ChaeyongPark-KU/HaptiCraft/Hardware/Thermal Module/3_side-left.STL

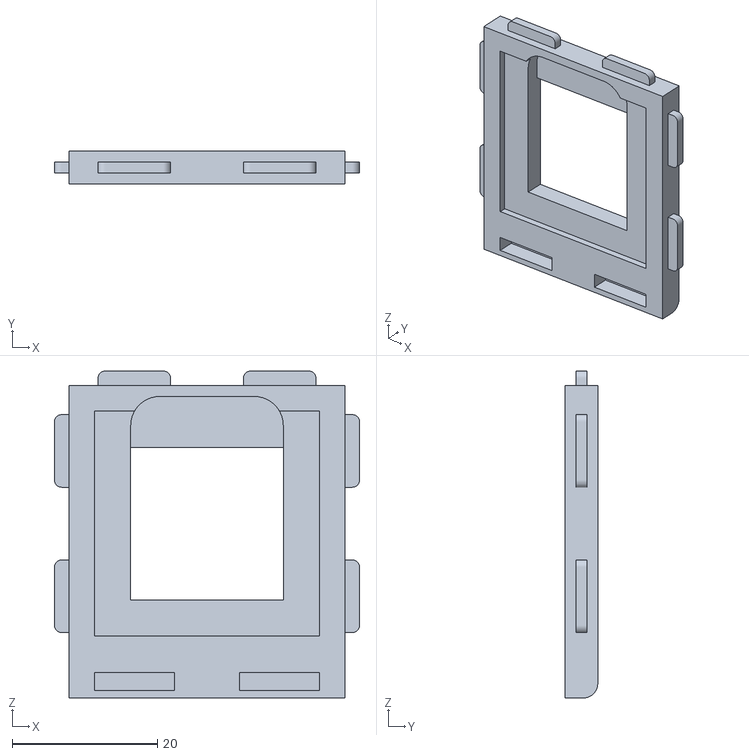
[picture p32: CAD file, 2026-03-29]
Hardware/Thermal Module/3_side-left.STL
42.0 x 4.50 x 45.0
