ChaeyongPark-KU/HaptiCraft/Hardware/Touch Module/3_touch pannel 1.STL

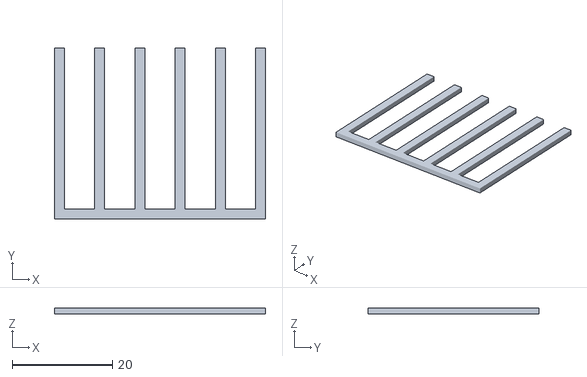
[picture p33: CAD file, 2026-03-29]
Hardware/Touch Module/3_touch pannel 1.STL
42.0 x 34.0 x 1.20
