ChaeyongPark-KU/HaptiCraft/Hardware/Tracking Module/3_rod 50mm.STL

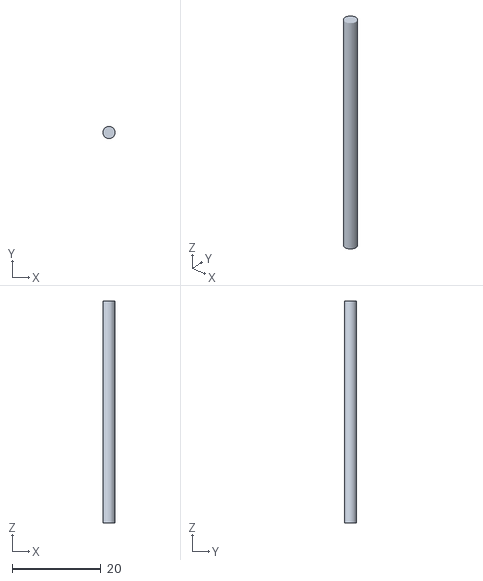
[picture p34: CAD file, 2026-03-29]
Hardware/Tracking Module/3_rod 50mm.STL
2.75 x 2.75 x 50.0
