ChaeyongPark-KU/HaptiCraft/Hardware/Variable Damping Actuator/5_plunger lower-part.STL

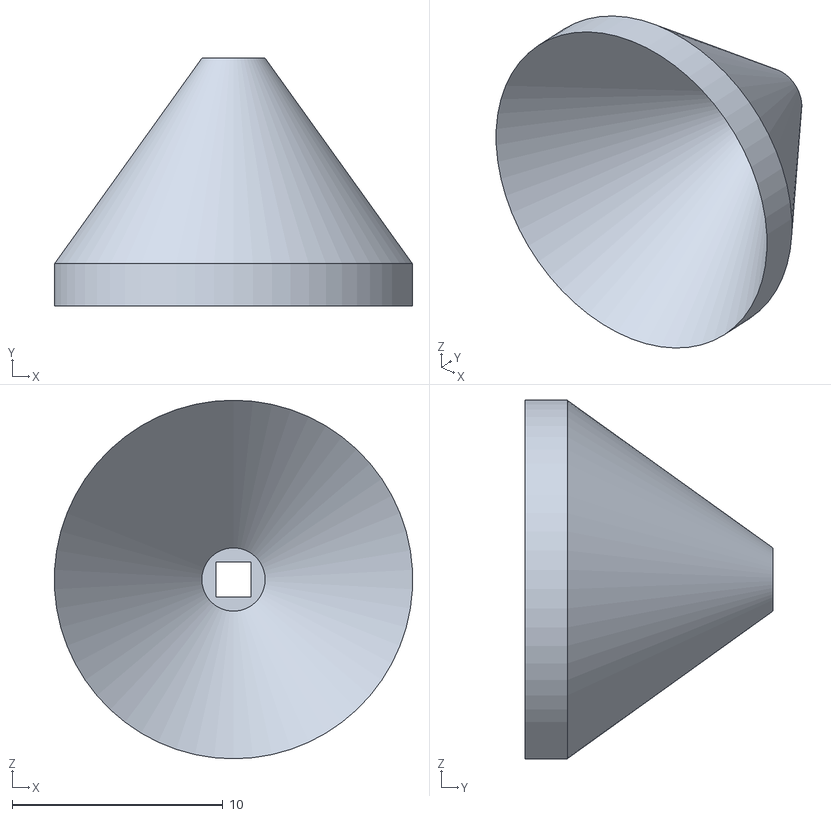
[picture p35: CAD file, 2026-03-31]
Hardware/Variable Damping Actuator/5_plunger lower-part.STL
17.0 x 11.8 x 17.0
