ChaeyongPark-KU/HaptiCraft/Hardware/Variable Inertia Module/8_internal circuit.STL

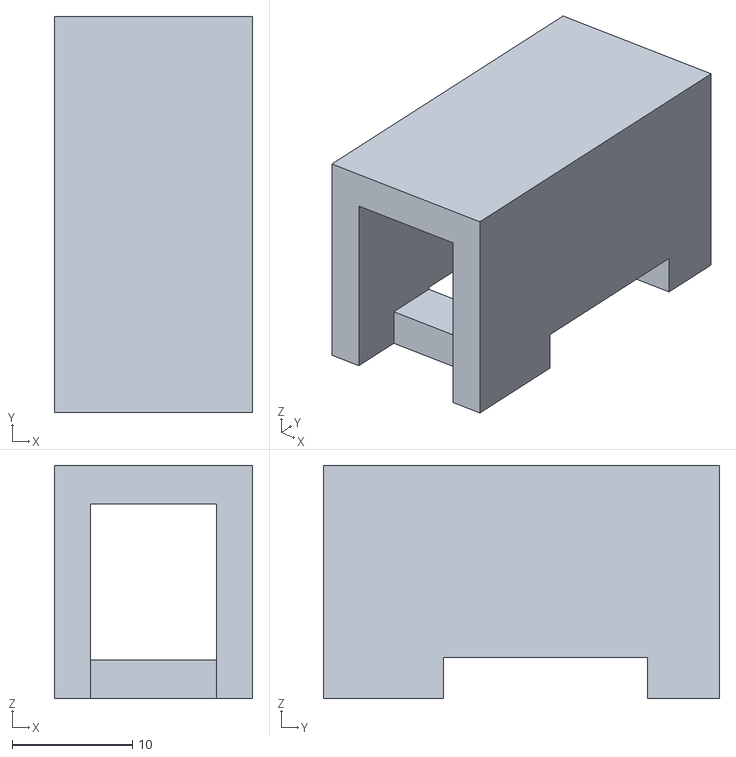
[picture p36: CAD file, 2026-03-29]
Hardware/Variable Inertia Module/8_internal circuit.STL
16.5 x 33.0 x 19.4
