ChaeyongPark-KU/HaptiCraft/Hardware/Vibration Module/2_side-front.STL

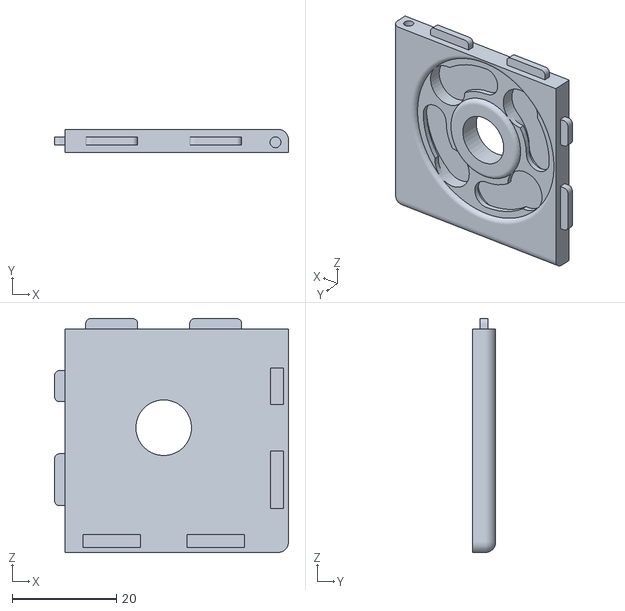
[picture p37: CAD file, 2026-03-29]
Hardware/Vibration Module/2_side-front.STL
45.0 x 4.50 x 45.0
