ChaeyongPark-KU/HaptiCraft/Hardware/Button Module/3_top.STL

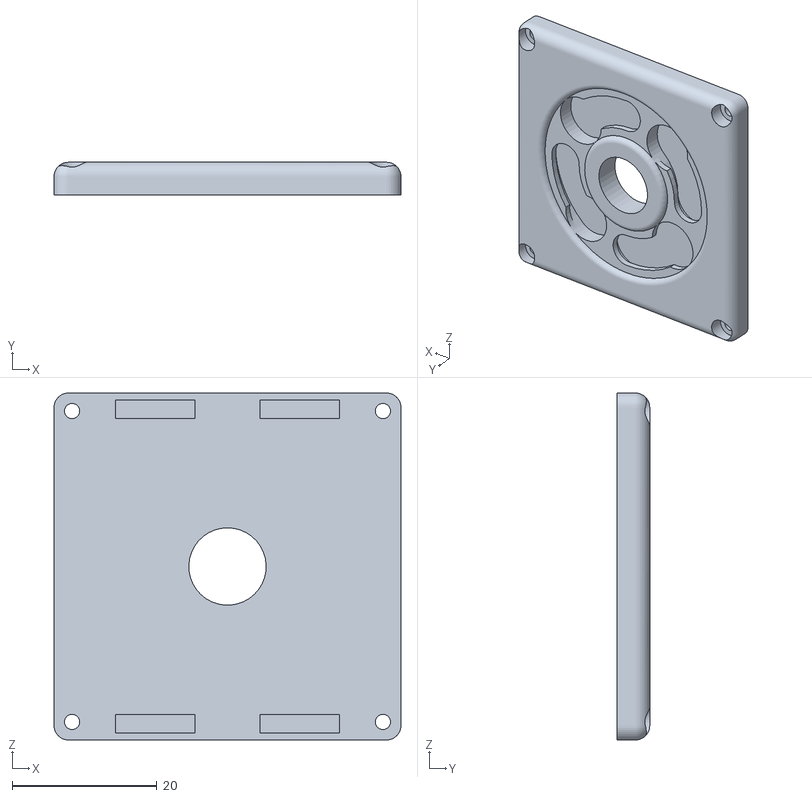
[picture p38: CAD file, 2026-03-29]
Hardware/Button Module/3_top.STL
48.0 x 4.50 x 48.0
