ChaeyongPark-KU/HaptiCraft/Hardware/Impact Module/6_top.STL

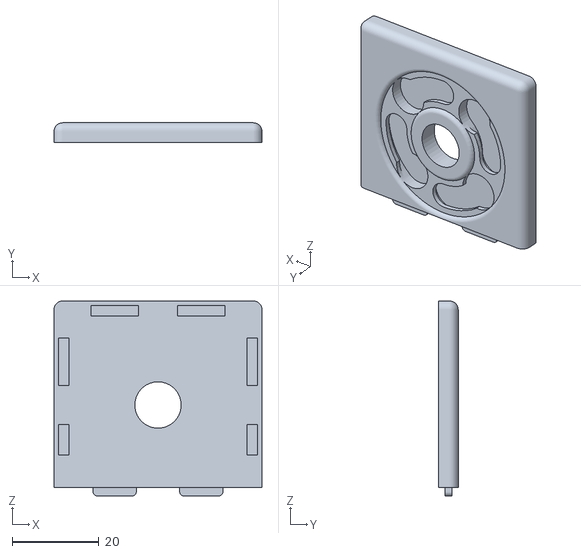
[picture p39: CAD file, 2026-03-29]
Hardware/Impact Module/6_top.STL
48.0 x 4.50 x 45.0
