ChaeyongPark-KU/HaptiCraft/Hardware/Power Module/1_bottom-single side.STL

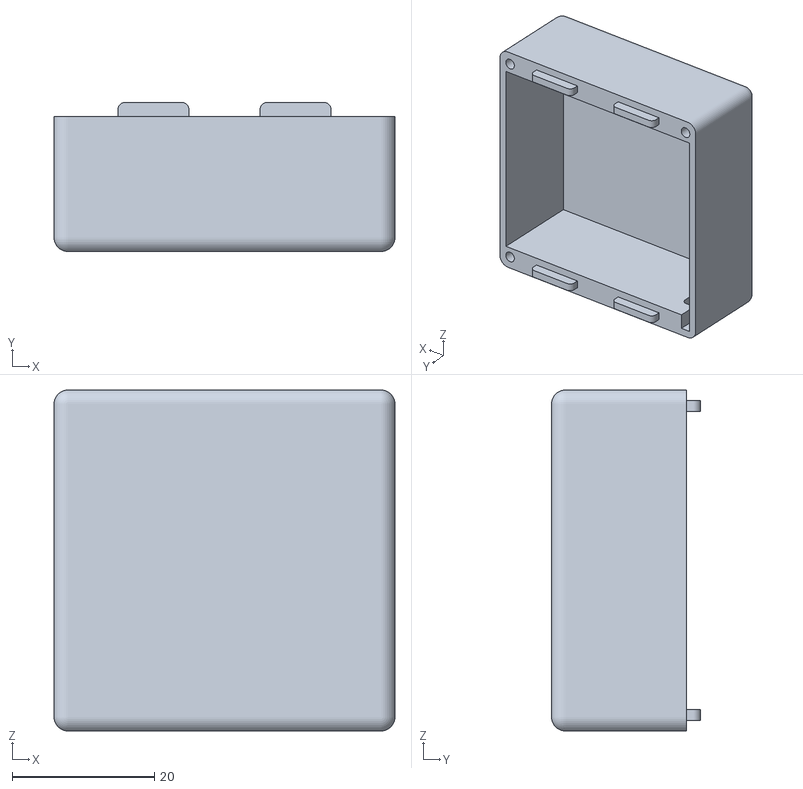
[picture p40: CAD file, 2026-03-29]
Hardware/Power Module/1_bottom-single side.STL
48.0 x 21.0 x 48.0
