ChaeyongPark-KU/HaptiCraft/Hardware/Shape Module/1_bottom.STL

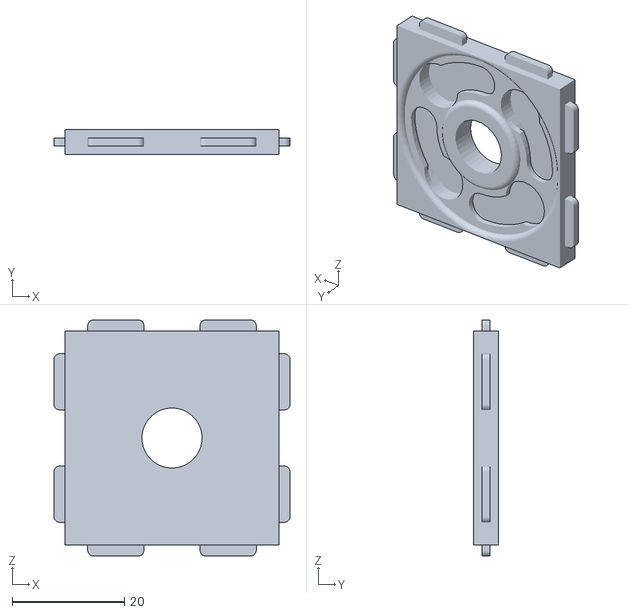
[picture p41: CAD file, 2026-03-29]
Hardware/Shape Module/1_bottom.STL
42.0 x 4.50 x 42.0
