ChaeyongPark-KU/HaptiCraft/Hardware/Thermal Module/4_side-back.STL

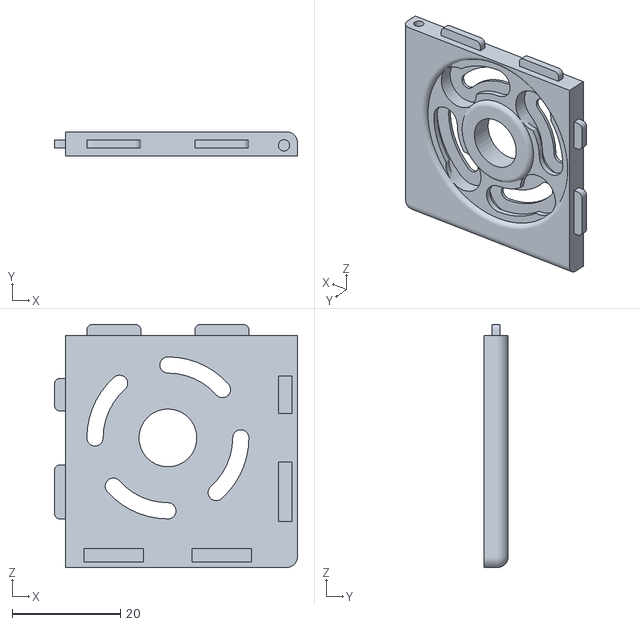
[picture p42: CAD file, 2026-03-29]
Hardware/Thermal Module/4_side-back.STL
45.0 x 4.50 x 45.0
