ChaeyongPark-KU/HaptiCraft/Hardware/Touch Module/4_touch pannel 2.STL

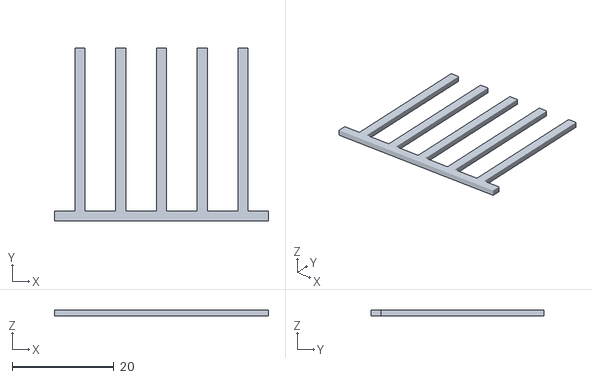
[picture p43: CAD file, 2026-03-29]
Hardware/Touch Module/4_touch pannel 2.STL
42.0 x 34.0 x 1.20
