ChaeyongPark-KU/HaptiCraft/Hardware/Tracking Module/2_rod 30mm.STL

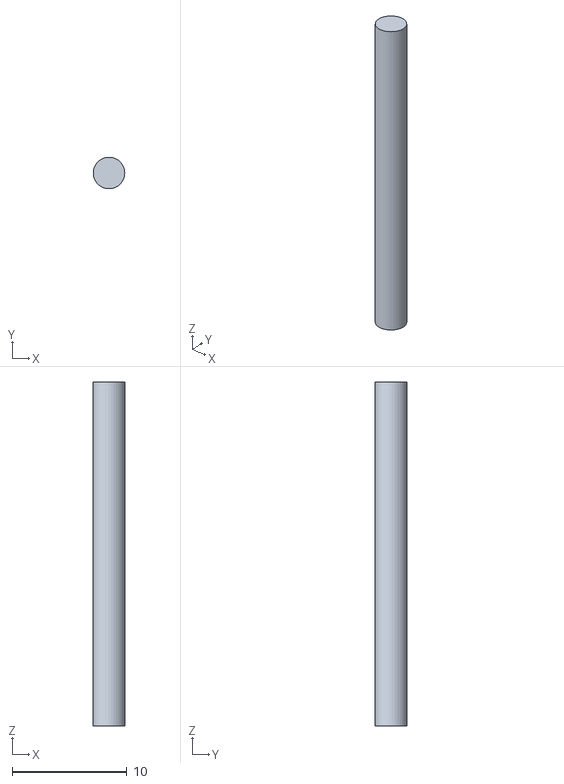
[picture p44: CAD file, 2026-03-29]
Hardware/Tracking Module/2_rod 30mm.STL
2.75 x 2.75 x 30.0
