ChaeyongPark-KU/HaptiCraft/Hardware/Variable Damping Actuator/4_plunger upper-part.STL

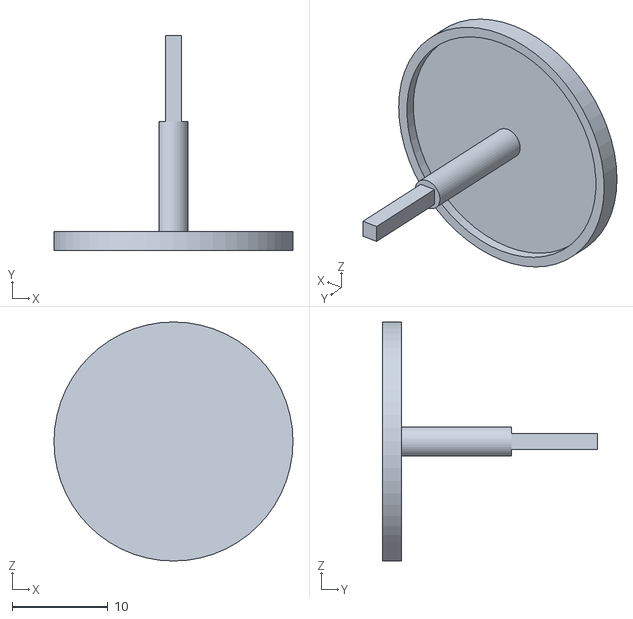
[picture p45: CAD file, 2026-03-31]
Hardware/Variable Damping Actuator/4_plunger upper-part.STL
25.0 x 22.5 x 25.0
