ChaeyongPark-KU/HaptiCraft/Hardware/Variable Stiffness Module/8_support.STL

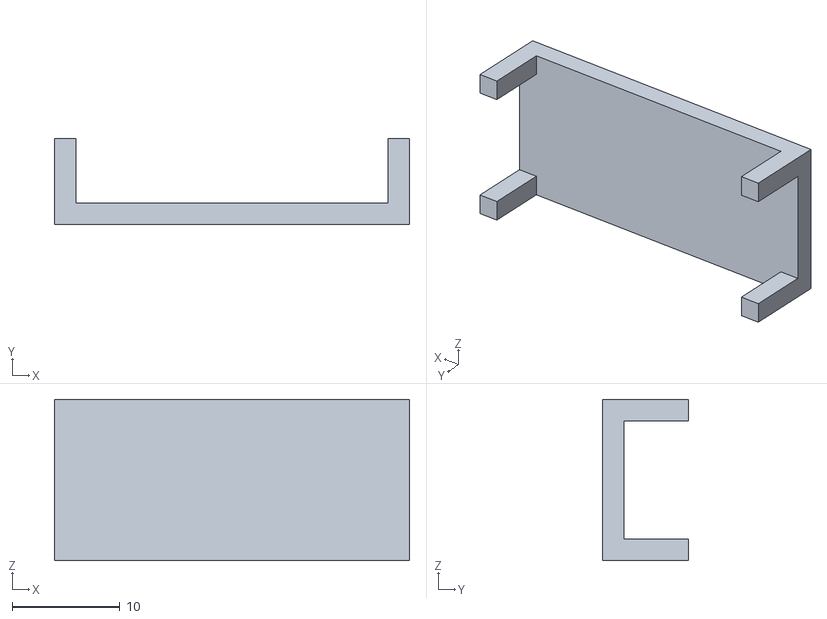
[picture p46: CAD file, 2026-03-29]
Hardware/Variable Stiffness Module/8_support.STL
33.0 x 8.00 x 15.0
