ChaeyongPark-KU/HaptiCraft/Hardware/Button Module/1_bottom.STL

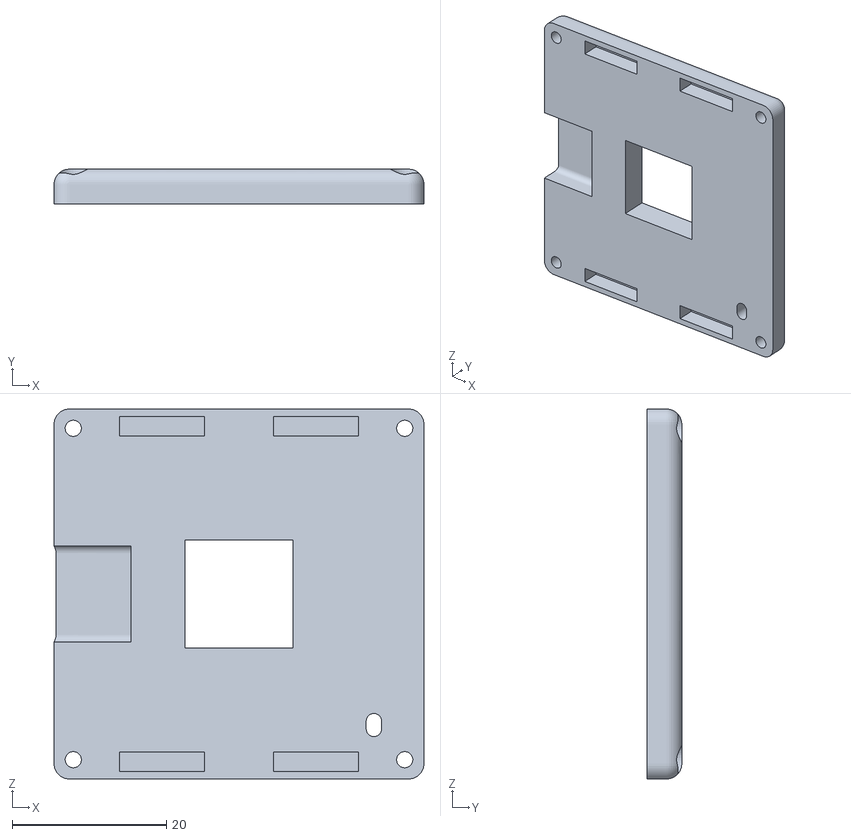
[picture p47: CAD file, 2026-03-29]
Hardware/Button Module/1_bottom.STL
48.0 x 4.50 x 48.0
