ChaeyongPark-KU/HaptiCraft/Hardware/Power Module/5_holder.STL

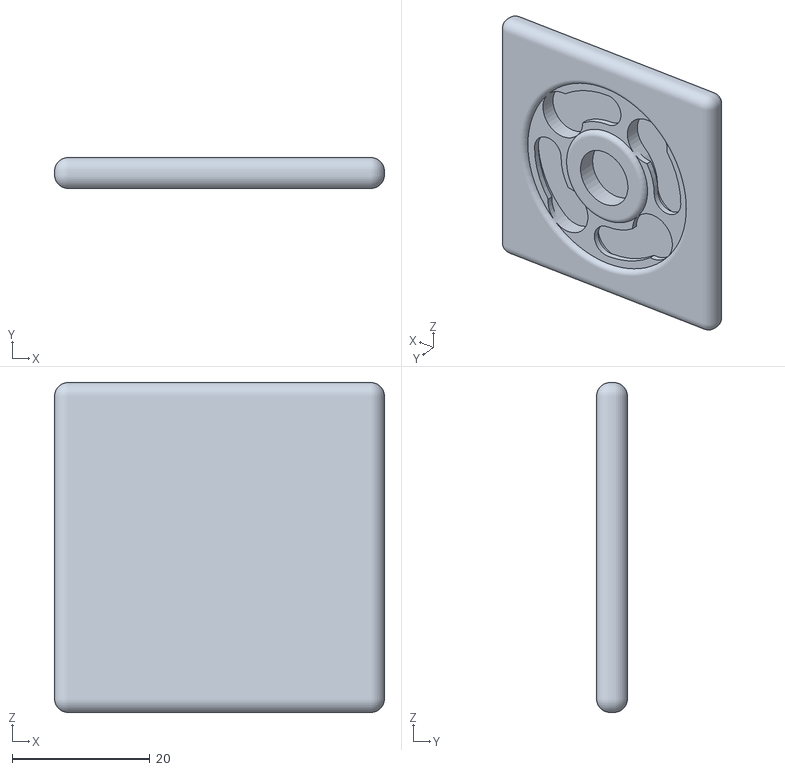
[picture p48: CAD file, 2026-03-29]
Hardware/Power Module/5_holder.STL
48.0 x 4.50 x 48.0
