ChaeyongPark-KU/HaptiCraft/Hardware/Thermal Module/1_bottom.STL

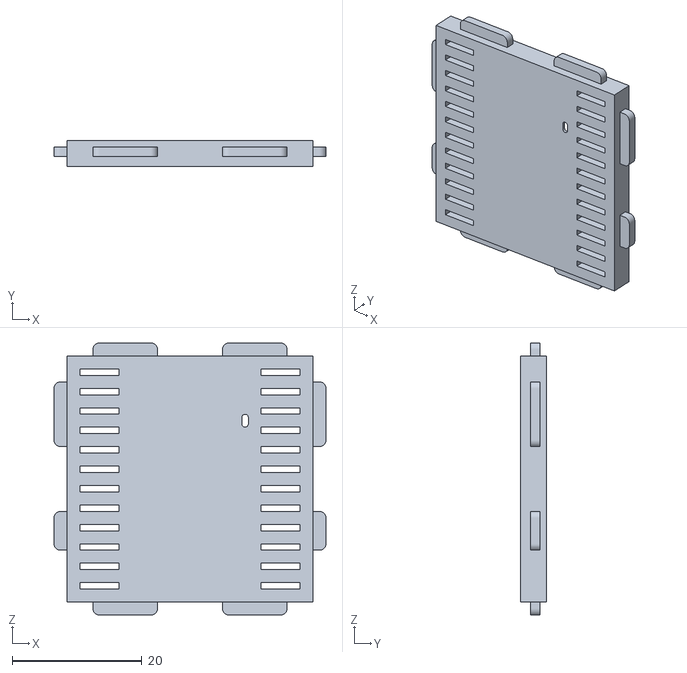
[picture p49: CAD file, 2026-03-29]
Hardware/Thermal Module/1_bottom.STL
42.0 x 4.00 x 42.0
