ChaeyongPark-KU/HaptiCraft/Hardware/Tracking Module/4_rod 70mm.STL

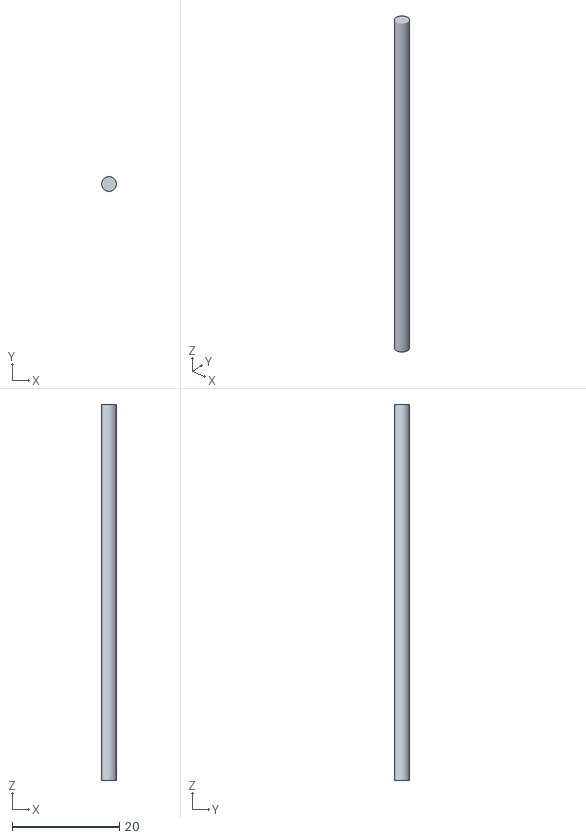
[picture p50: CAD file, 2026-03-29]
Hardware/Tracking Module/4_rod 70mm.STL
2.75 x 2.75 x 70.0
