ChaeyongPark-KU/HaptiCraft/Hardware/Variable Damping Actuator/3_coil.STL

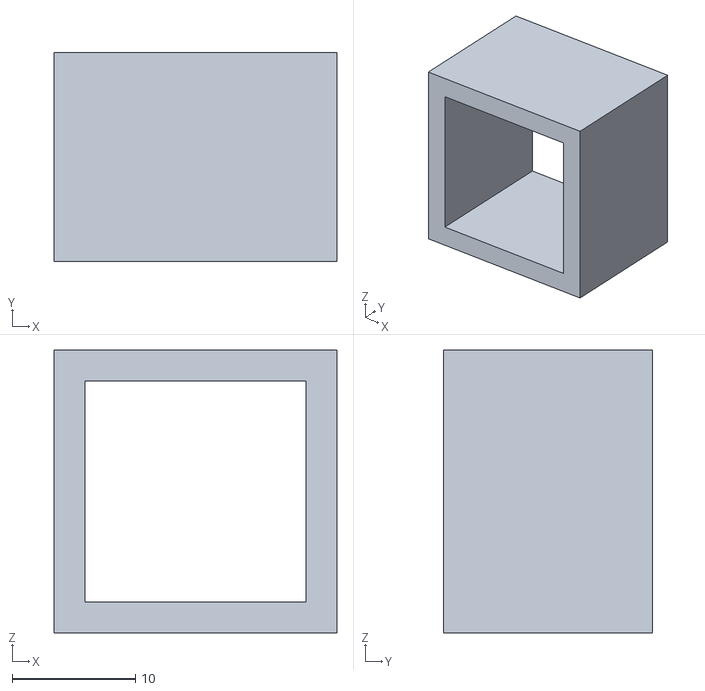
[picture p51: CAD file, 2026-03-31]
Hardware/Variable Damping Actuator/3_coil.STL
23.0 x 17.0 x 23.0
