ChaeyongPark-KU/HaptiCraft/Hardware/Variable Inertia Module/10_moving mass ring.STL

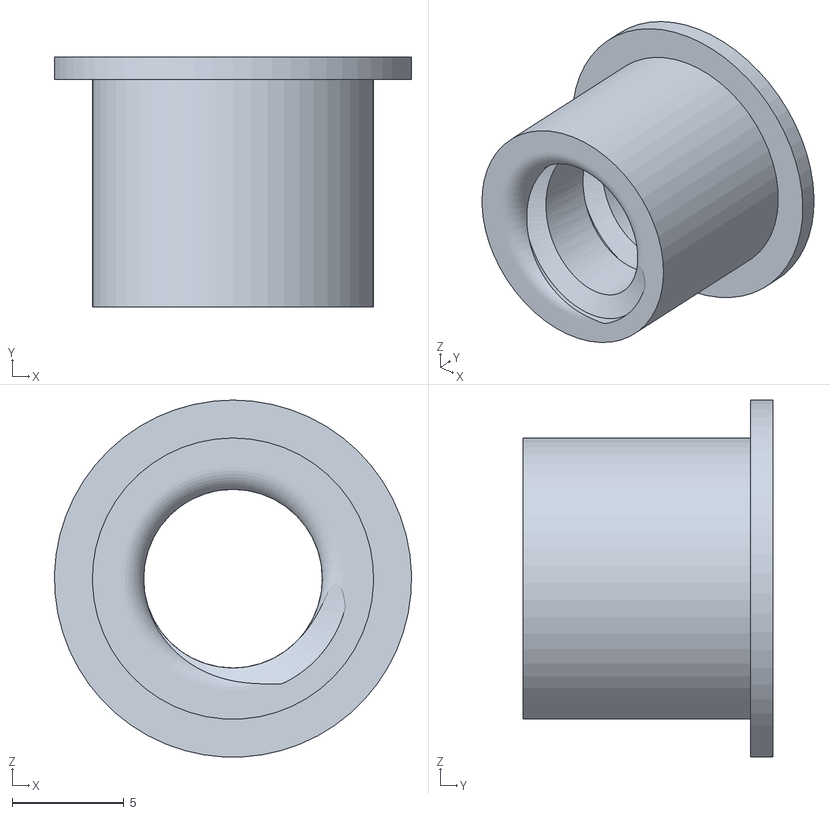
[picture p52: CAD file, 2026-03-29]
Hardware/Variable Inertia Module/10_moving mass ring.STL
16.0 x 11.2 x 16.0
