ChaeyongPark-KU/HaptiCraft/Hardware/Variable Stiffness Module/2_side-front.STL

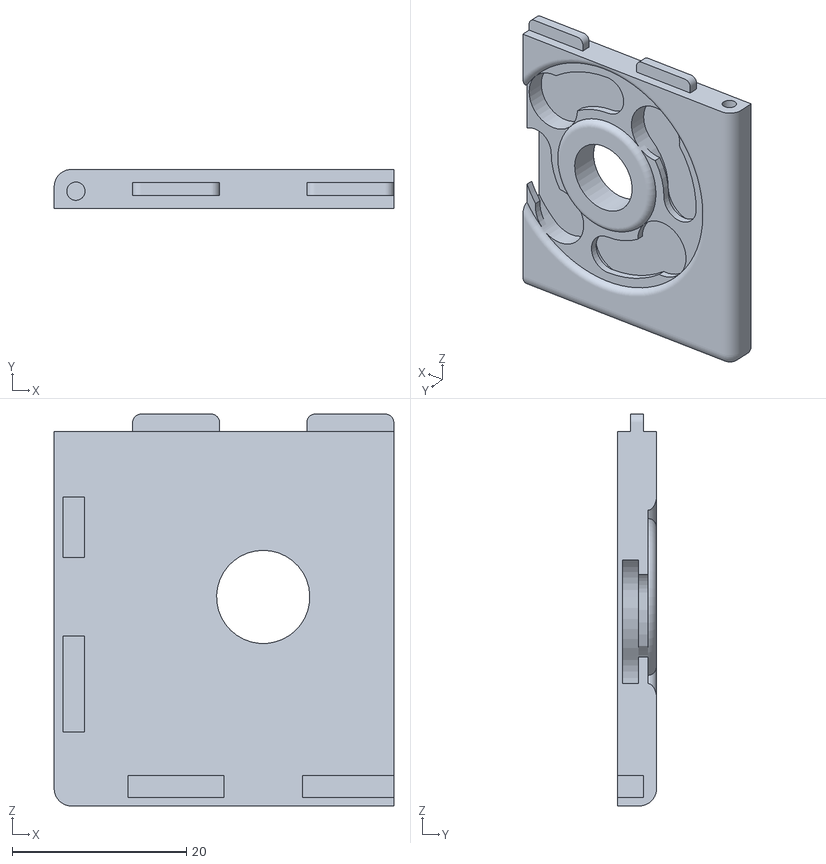
[picture p53: CAD file, 2026-03-29]
Hardware/Variable Stiffness Module/2_side-front.STL
39.0 x 4.50 x 45.0
