ChaeyongPark-KU/HaptiCraft/Hardware/Power Module/2_bottom-double side.STL

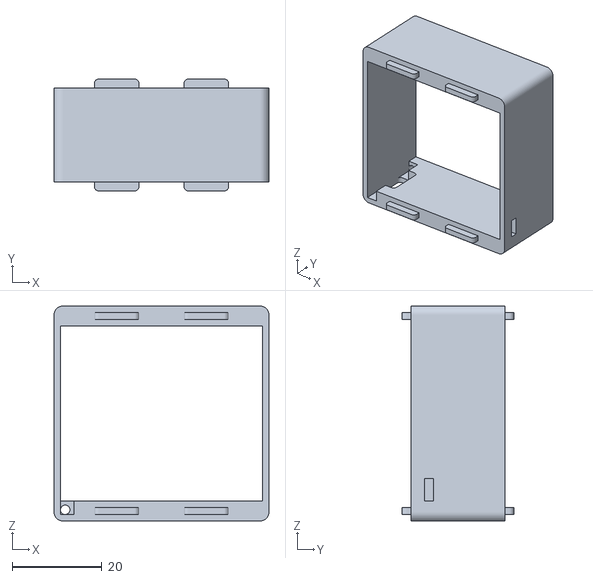
[picture p54: CAD file, 2026-03-29]
Hardware/Power Module/2_bottom-double side.STL
48.0 x 25.0 x 48.0
