ChaeyongPark-KU/HaptiCraft/Hardware/Thermal Module/7_support.STL

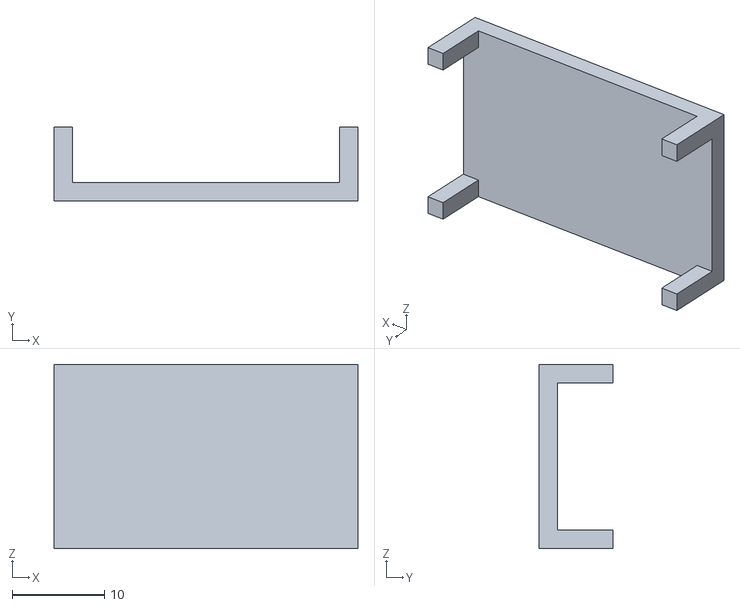
[picture p55: CAD file, 2026-03-29]
Hardware/Thermal Module/7_support.STL
33.0 x 8.00 x 20.0
