ChaeyongPark-KU/HaptiCraft/Hardware/Tracking Module/1_bottom.STL

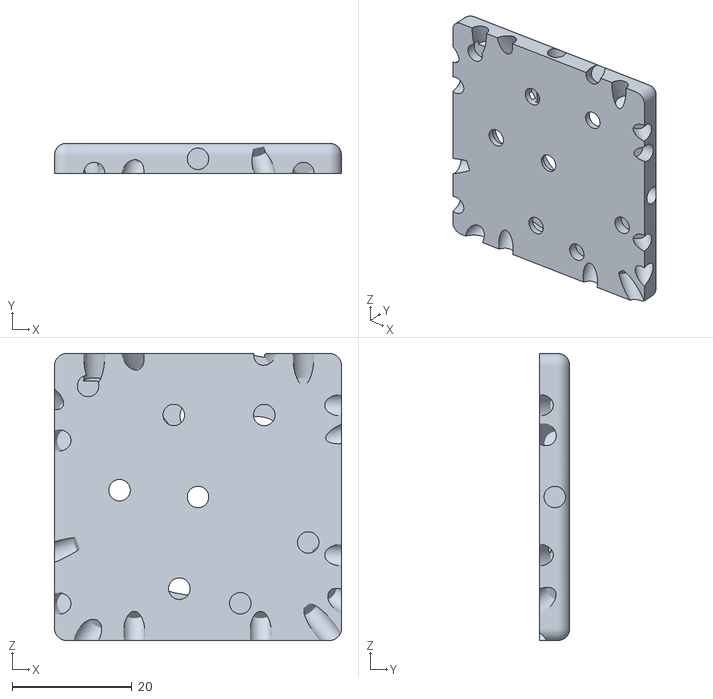
[picture p56: CAD file, 2026-03-29]
Hardware/Tracking Module/1_bottom.STL
48.0 x 5.10 x 48.0
