ChaeyongPark-KU/HaptiCraft/Hardware/Variable Damping Actuator/6_housing upper-part.STL

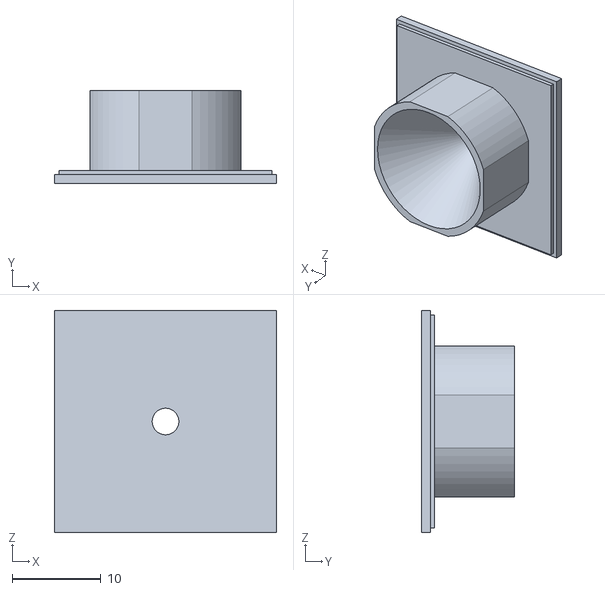
[picture p57: CAD file, 2026-03-31]
Hardware/Variable Damping Actuator/6_housing upper-part.STL
25.0 x 10.5 x 25.0
