ChaeyongPark-KU/HaptiCraft/Hardware/Variable Inertia Module/6_top.STL

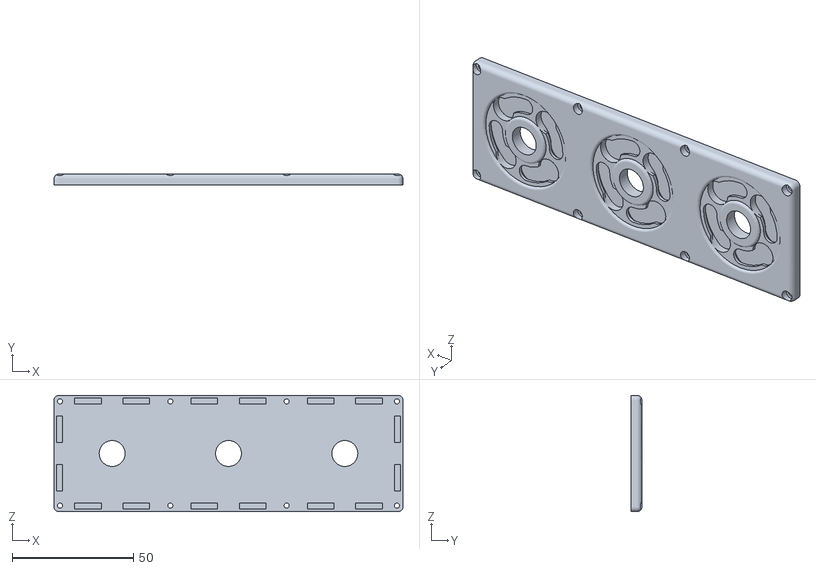
[picture p58: CAD file, 2026-03-29]
Hardware/Variable Inertia Module/6_top.STL
144.0 x 4.50 x 48.0
