ChaeyongPark-KU/HaptiCraft/Hardware/Variable Stiffness Module/6_top.STL

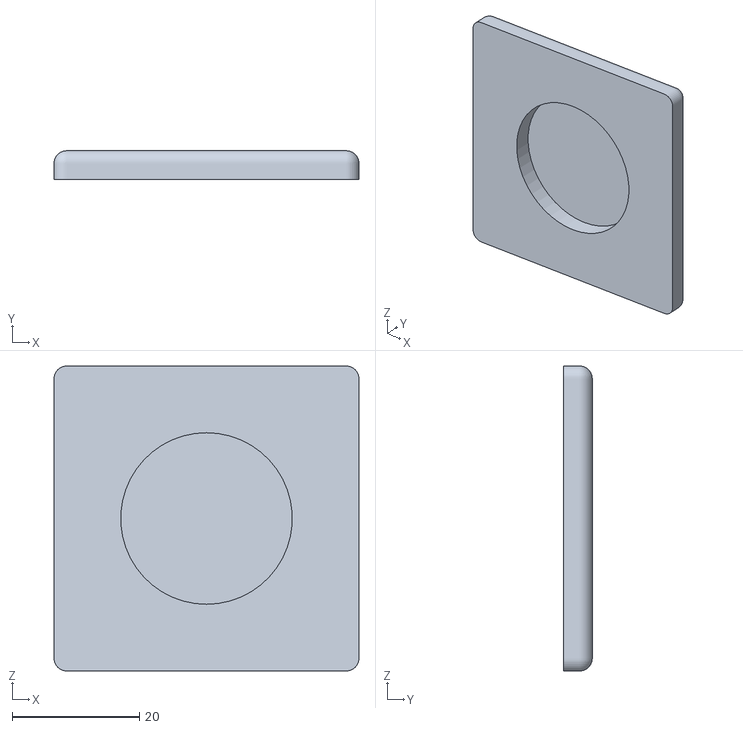
[picture p59: CAD file, 2026-03-29]
Hardware/Variable Stiffness Module/6_top.STL
48.0 x 4.50 x 48.0
