ChaeyongPark-KU/HaptiCraft/Hardware/Vibration Module/5_side-right.STL

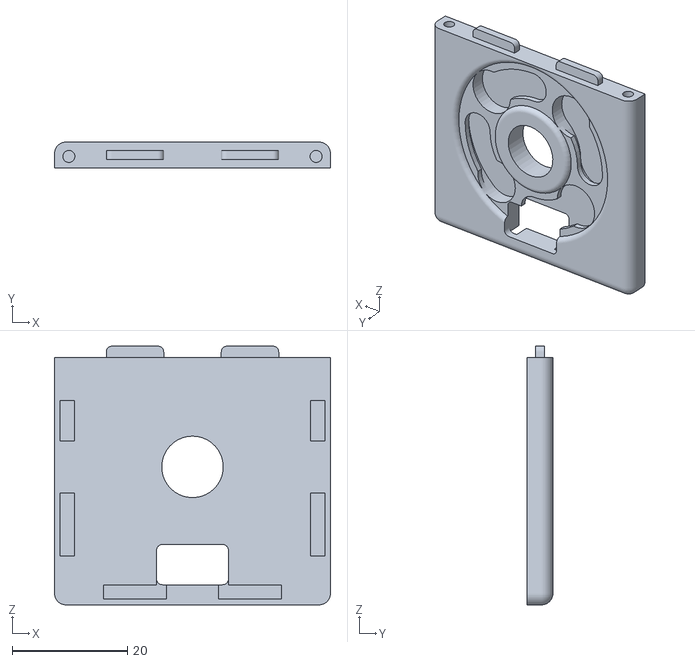
[picture p60: CAD file, 2026-03-29]
Hardware/Vibration Module/5_side-right.STL
48.0 x 4.50 x 45.0
