ChaeyongPark-KU/HaptiCraft/Hardware/Variable Damping Actuator/2_spring.STL

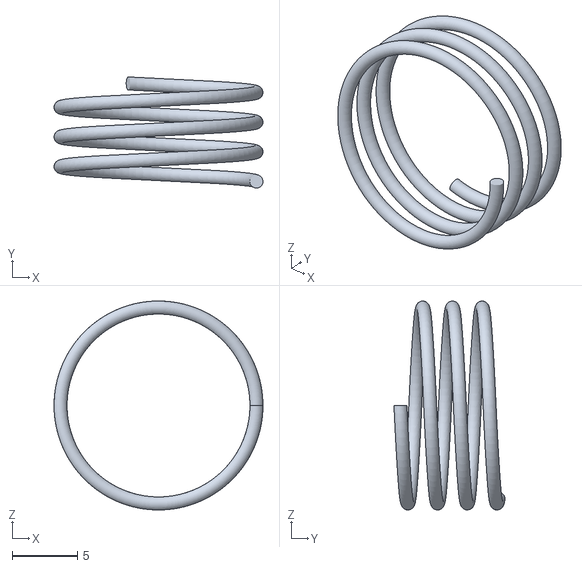
[picture p62: CAD file, 2026-03-31]
Hardware/Variable Damping Actuator/2_spring.STL
16.0 x 8.51 x 16.0
