ChaeyongPark-KU/HaptiCraft/Hardware/Variable Stiffness Module/5_side-right.STL

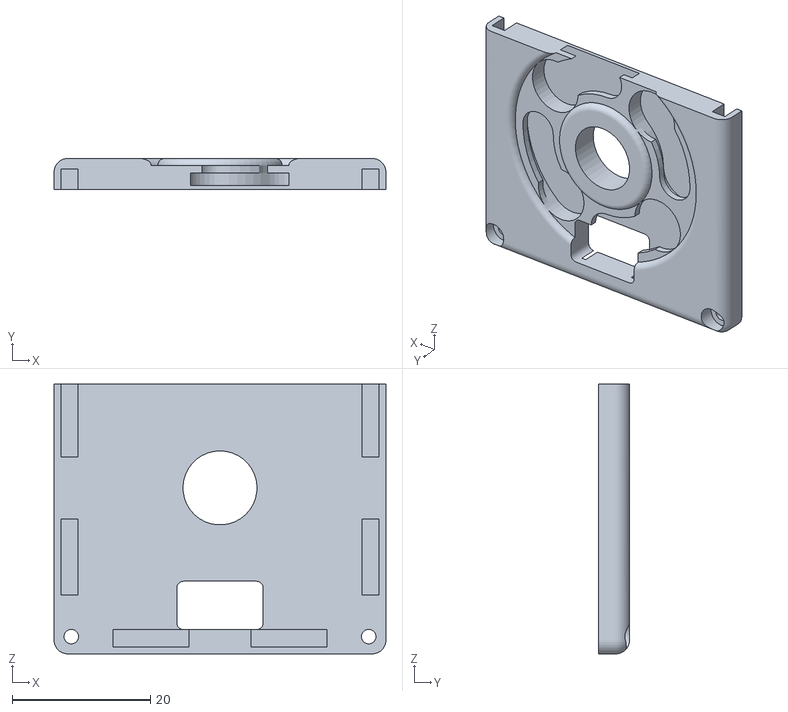
[picture p63: CAD file, 2026-03-29]
Hardware/Variable Stiffness Module/5_side-right.STL
48.0 x 4.50 x 39.0
