ChaeyongPark-KU/HaptiCraft/Hardware/Variable Damping Actuator/7_housing lower-part.STL

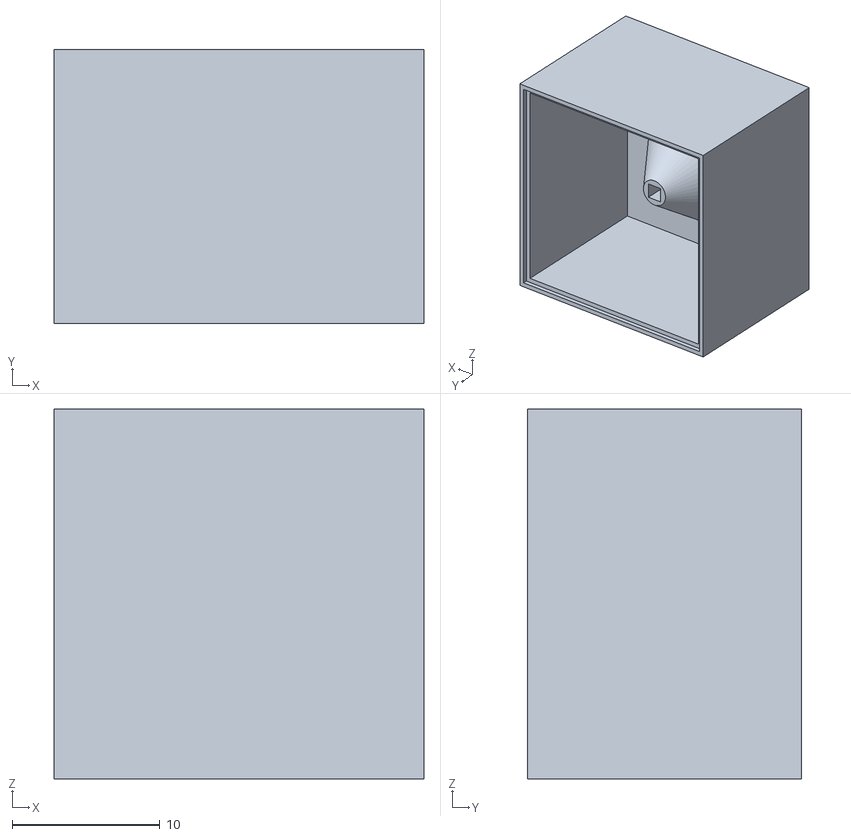
[picture p64: CAD file, 2026-03-31]
Hardware/Variable Damping Actuator/7_housing lower-part.STL
25.0 x 18.5 x 25.0
