ChaeyongPark-KU/HaptiCraft/Hardware/Variable Inertia Module/4_side-back.STL

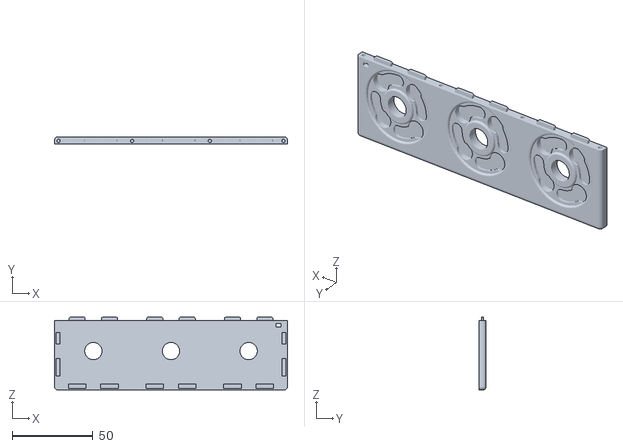
[picture p65: CAD file, 2026-03-29]
Hardware/Variable Inertia Module/4_side-back.STL
144.0 x 4.50 x 45.0
