ChaeyongPark-KU/HaptiCraft/Hardware/Variable Stiffness Module/7_button holder.STL

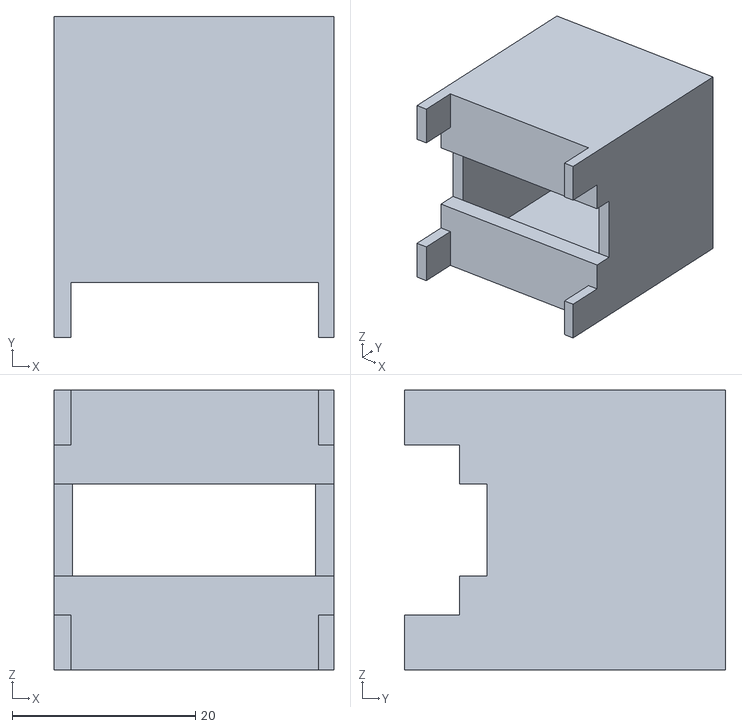
[picture p66: CAD file, 2026-03-29]
Hardware/Variable Stiffness Module/7_button holder.STL
30.5 x 35.0 x 30.5
