ChaeyongPark-KU/HaptiCraft/Hardware/Vibration Module/7_support.STL

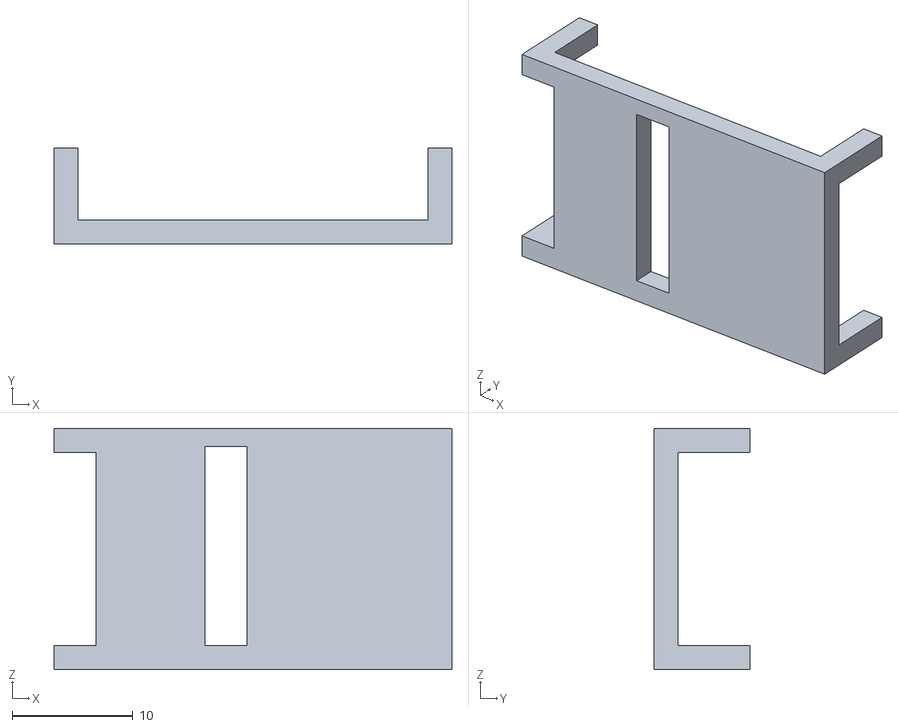
[picture p67: CAD file, 2026-03-29]
Hardware/Vibration Module/7_support.STL
33.0 x 8.00 x 20.0
