ChaeyongPark-KU/HaptiCraft/Hardware/Variable Damping Actuator/1_spring base.STL

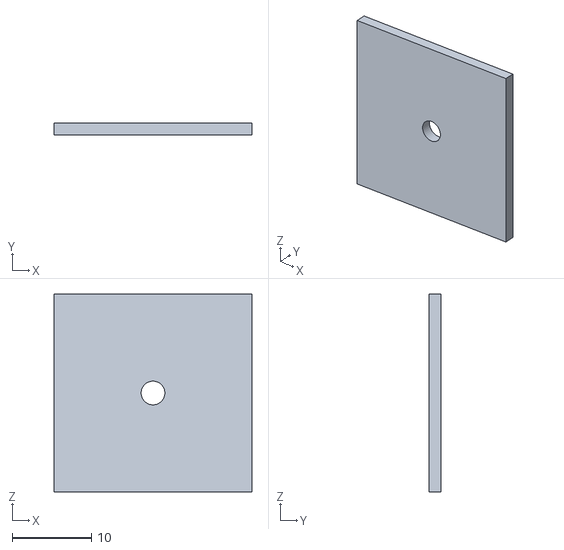
[picture p68: CAD file, 2026-03-31]
Hardware/Variable Damping Actuator/1_spring base.STL
25.0 x 1.50 x 25.0
