ChaeyongPark-KU/HaptiCraft/Hardware/Variable Inertia Module/7_top-ring.STL

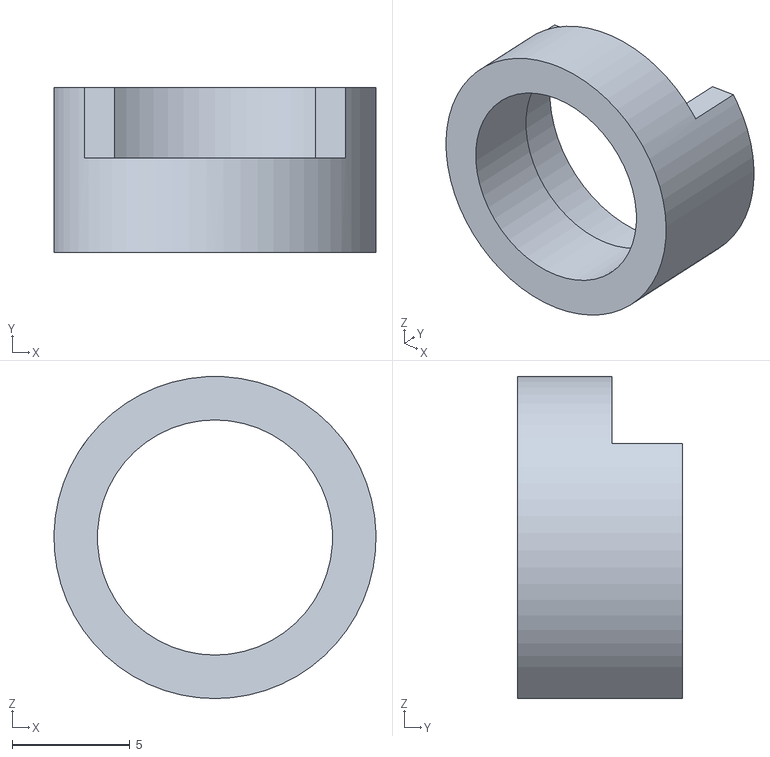
[picture p69: CAD file, 2026-03-29]
Hardware/Variable Inertia Module/7_top-ring.STL
13.7 x 7.00 x 13.7
