ChaeyongPark-KU/HaptiCraft/Hardware/Variable Stiffness Module/4_side-back.STL

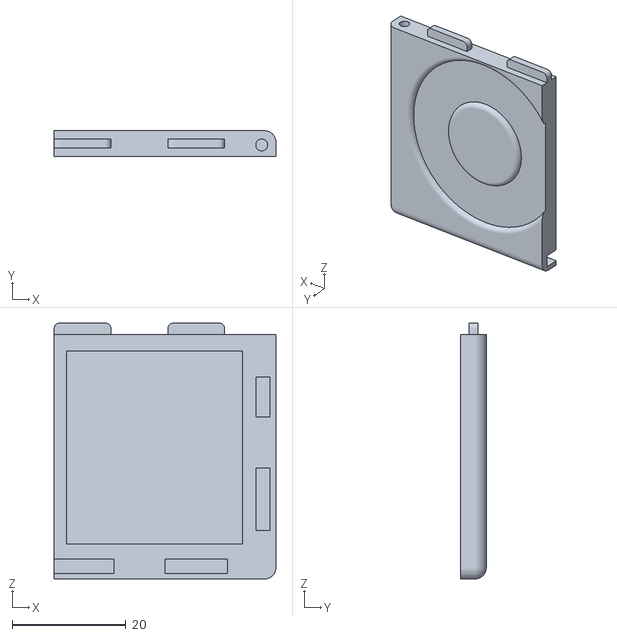
[picture p70: CAD file, 2026-03-29]
Hardware/Variable Stiffness Module/4_side-back.STL
39.0 x 4.50 x 45.0
