ChaeyongPark-KU/HaptiCraft/Hardware/Variable Inertia Module/5_side-right.STL

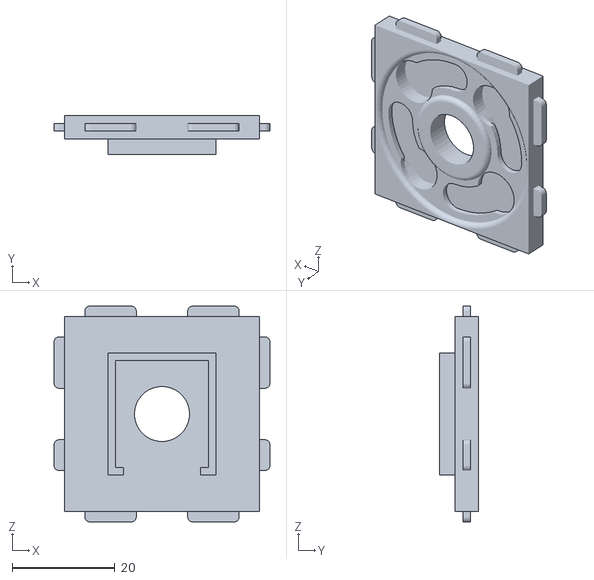
[picture p71: CAD file, 2026-03-29]
Hardware/Variable Inertia Module/5_side-right.STL
42.0 x 7.50 x 42.0
