ChaeyongPark-KU/HaptiCraft/Hardware/Variable Inertia Module/9_moving mass.STL

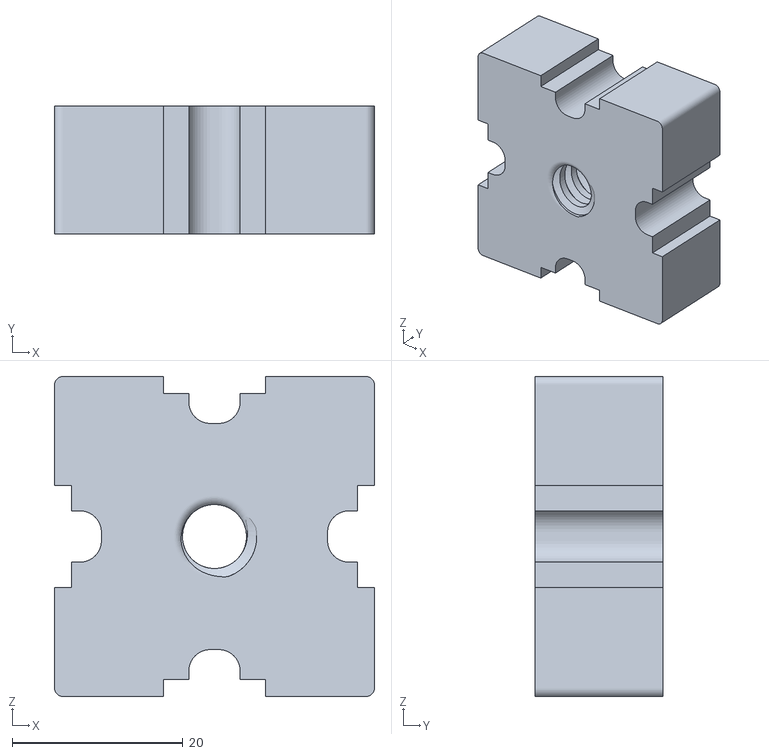
[picture p72: CAD file, 2026-03-29]
Hardware/Variable Inertia Module/9_moving mass.STL
37.5 x 15.0 x 37.5
